DIYSynthMNL/Eurorack-3340-VCO/kicad/3340-VCO.kicad_pcb

## KiCad design schematic/Kicad/si4825_Narrow_Wide_Band_setup/si4825_Narrow_Wide_Band_setup.kicad_sch

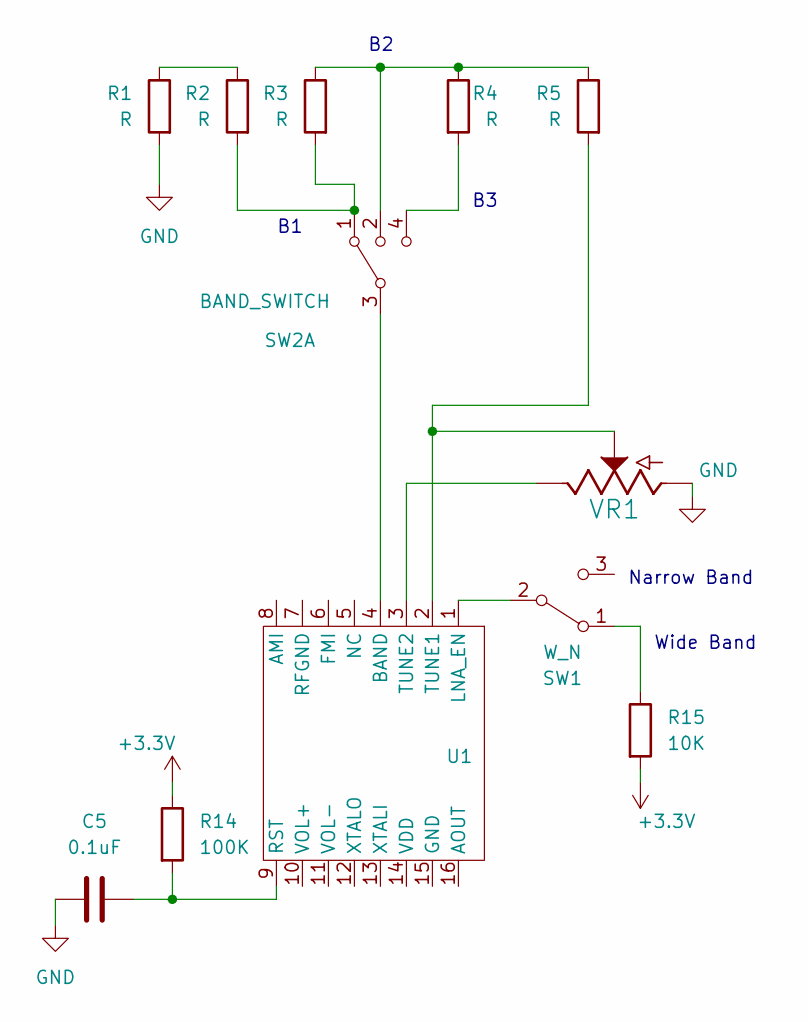
[picture p9: schematic si4825_Narrow_Wide_Band_setup.kicad_sch]

Parts:
C5: 0.1uF
R1, R2, R3, R4, R5: R
R14: 100K
R15: 10K
SW1: W_N
SW2: BAND_SWITCH
U1: SI4825
VR1: 100K; POT-PTH-ALPS

Connections:
+3.3V: R14.1, R15.2
GND: C5.2, R1.2, VR1.P$3 (A)
unnamed: C5.1, R14.2, U1.9 (RST)
unnamed: R1.1, R2.1
unnamed: R2.2, R3.2, SW2.1
unnamed: R3.1, R4.1, R5.1, SW2.2
unnamed: R4.2, SW2.4
unnamed: R5.2, U1.2 (TUNE1), VR1.P$2 (S)
unnamed: R15.1, SW1.1 (A)
unnamed: SW1.2 (B), U1.1 (LNA_EN)
unnamed: SW2.3, U1.4 (BAND)
unnamed: U1.3 (TUNE2), VR1.P$1 (E)

Notes on the sheet:
Wide Band
Narrow Band
