DIYSynthMNL/Eurorack-3340-VCO/kicad/3340-VCO.kicad_pcb

## KiCad design schematic/Kicad/si4825_band_setup_example/si4825_band_setup_example.kicad_sch

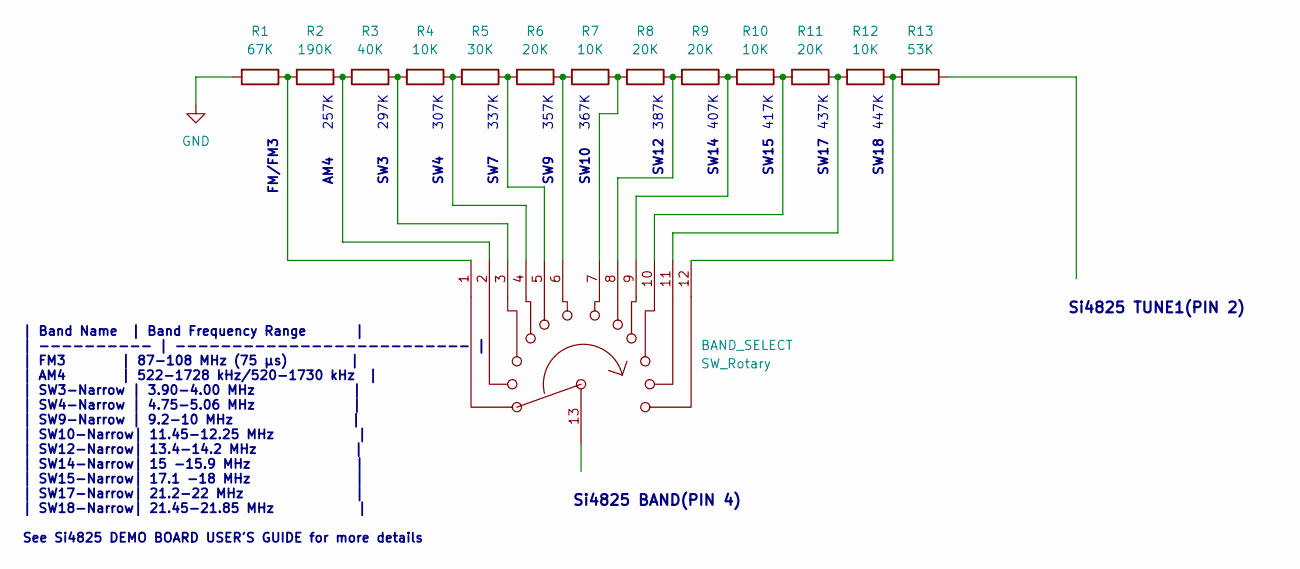
[picture p10: schematic si4825_band_setup_example.kicad_sch]

Parts:
BAND_SELECT: SW_Rotary
R1: 67K
R2: 190K
R3: 40K
R4, R7, R10, R12: 10K
R5: 30K
R6, R8, R9, R11: 20K
R13: 53K

Connections:
GND: R1.2
unnamed: BAND_SELECT.1, R1.1, R2.2
unnamed: BAND_SELECT.2, R2.1, R3.2
unnamed: BAND_SELECT.3, R3.1, R4.2
unnamed: BAND_SELECT.4, R4.1, R5.2
unnamed: BAND_SELECT.5, R5.1, R6.2
unnamed: BAND_SELECT.6, R6.1, R7.2
unnamed: BAND_SELECT.7, R7.1, R8.2
unnamed: BAND_SELECT.8, R8.1, R9.2
unnamed: BAND_SELECT.9, R9.1, R10.2
unnamed: BAND_SELECT.10, R10.1, R11.2
unnamed: BAND_SELECT.11, R11.1, R12.2
unnamed: BAND_SELECT.12, R12.1, R13.2

Notes on the sheet:
SW7
447K
437K
367K
Si4825 TUNE1(PIN 2)
Si4825 BAND(PIN 4)
337K
SW15
SW12
417K
SW9
SW18
AM4
297K
357K
407K
SW4
307K
| Band Name | Band Frequency Range | | ---------- | -------------------------- | | FM3 | 87-108 MHz (75 µs) | | AM4 | 522-1728 kHz/520-1730 kHz | | SW3-Narrow | 3.90-4.00 MHz | | SW4-Narrow | 4.75-5.06 MHz | | SW9-Narrow | 9.2-10 MHz | | SW10-Narrow| 11.45-12.25 MHz | | SW12-Narrow| 13.4-14.2 MHz |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
387K
SW17
257K
SW14
FM/FM3
SW3
SW10
